ketoglou/soldering_station/Firmware/Soldering_station_hakko_907.X/init_strings.h

#ifndef INIT_STRINGS_H
#define INIT_STRINGS_H

CHAR keto_st[12] = { SPACE,K,E,T,O,SPACE,H,A,K,K,O,SPACE };
byte hakko_num[3] = { 9,0,7 };
CHAR sold_station[16] = { SIGMA,T,A,THETA,M,O,SIGMA,SPACE,K,O,LAMDA,LAMDA,I,SIGMA,H,SIGMA};
CHAR temperature[12] = { THETA,E,P,M,O,K,P,A,SIGMA,I,A,COLON };
CHAR set[11] = { O,P,I,SIGMA,M,E,N,H,SPACE,SPACE,COLON };
CHAR real[11] = { PI,P,A,GAMMA,M,A,T,I,K,H,COLON };
CHAR celsious[2] = { DEGREE,CELSIOUS };

#endif
